alexia-maholea/OpenBook_TSC/Images/baterie.png

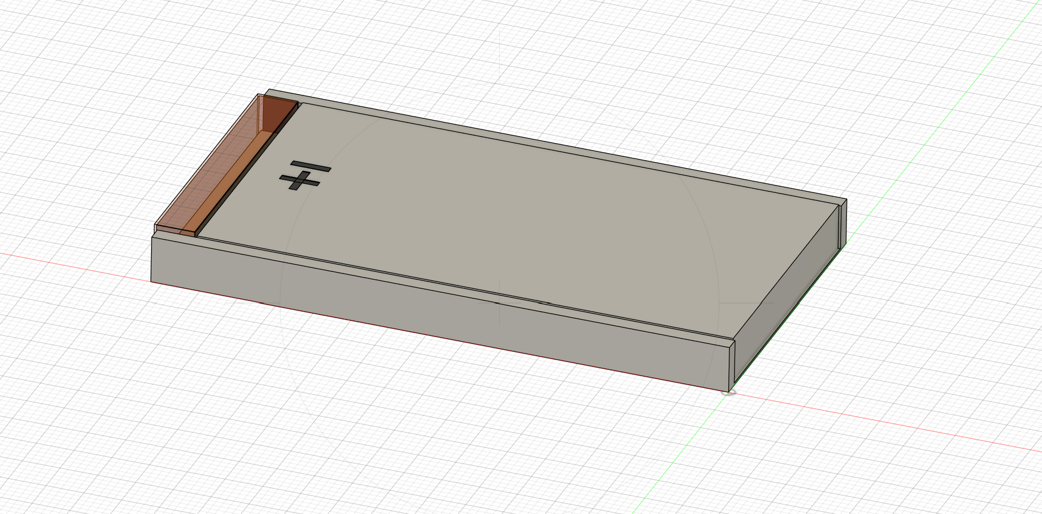
Images/baterie.png
