alexia-maholea/OpenBook_TSC/Images/display.png

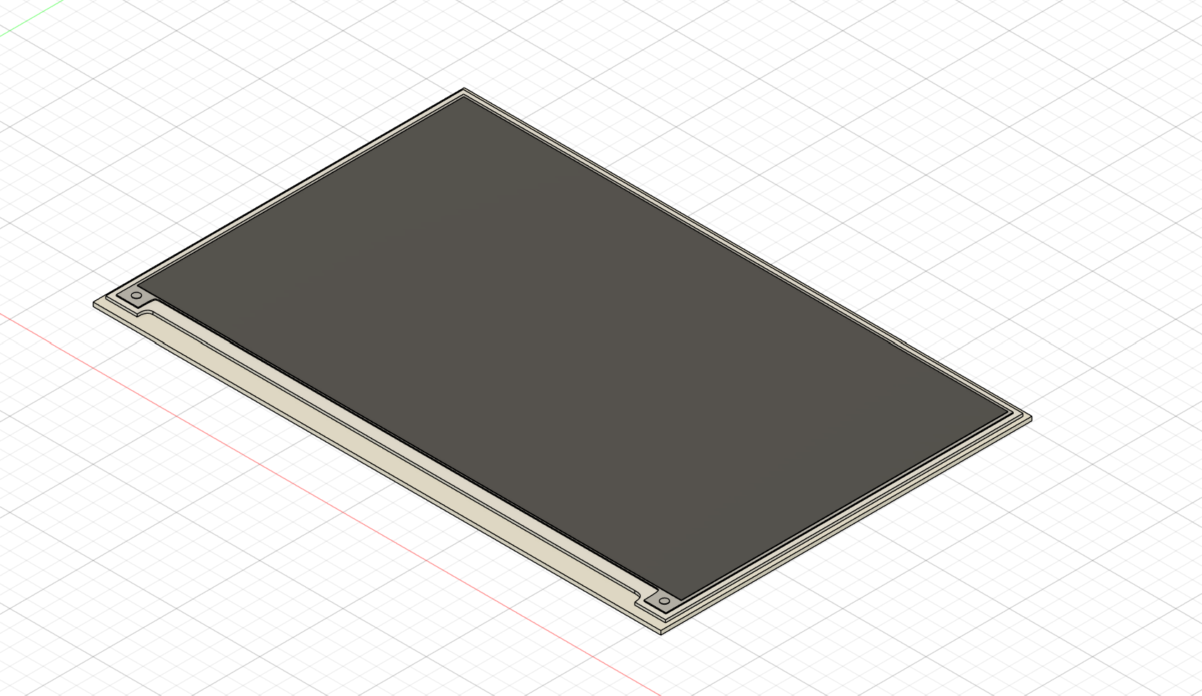
Images/display.png
